FerCanAra/Ce2Lab_ball_and_beam/Ball and Beam/Model 1/images/image 3.jpeg

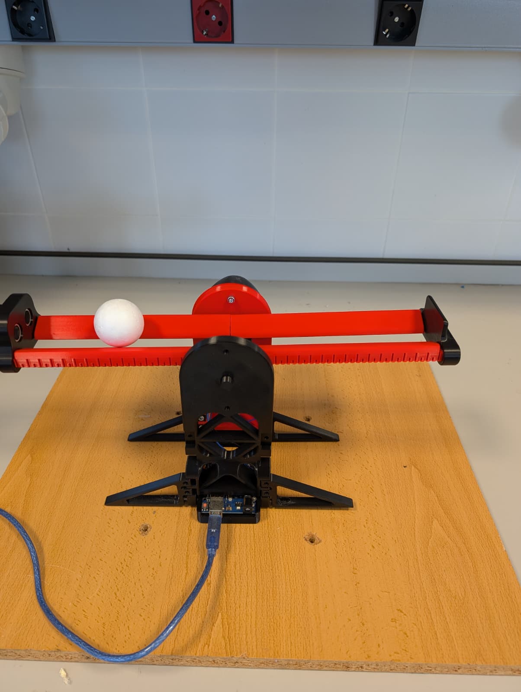
Ball and Beam/Model 1/images/image 3.jpeg
