FerCanAra/Ce2Lab_ball_and_beam/Ball and Beam/Model 1/images/image 7.jpeg

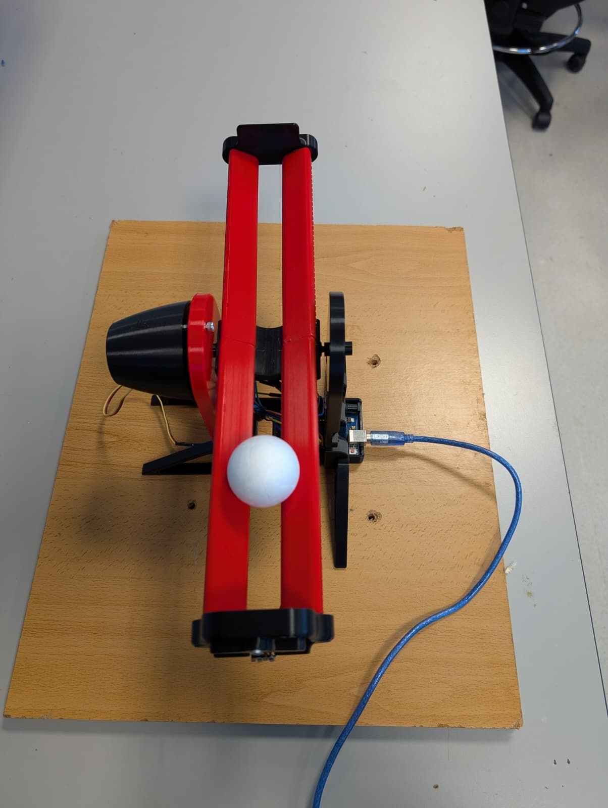
Ball and Beam/Model 1/images/image 7.jpeg
