FerCanAra/Ce2Lab_ball_and_beam/Ball and Beam/Model 1/images/info_3.png

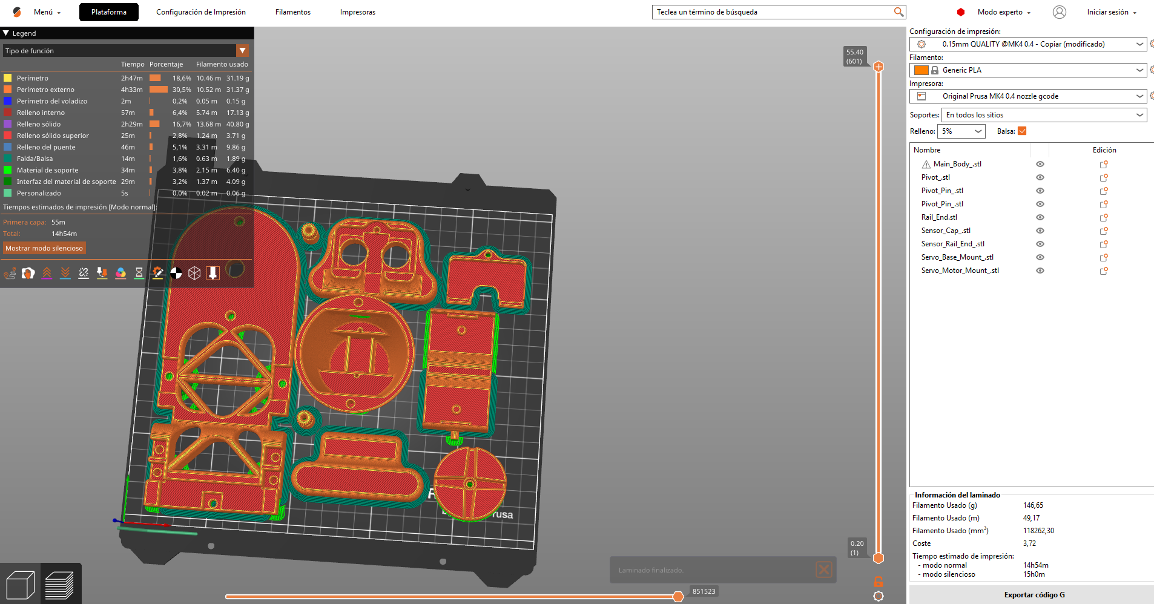
Ball and Beam/Model 1/images/info_3.png
