FerCanAra/Ce2Lab_ball_and_beam/Ball and Beam/Model 2/image/model_2_prusa.png

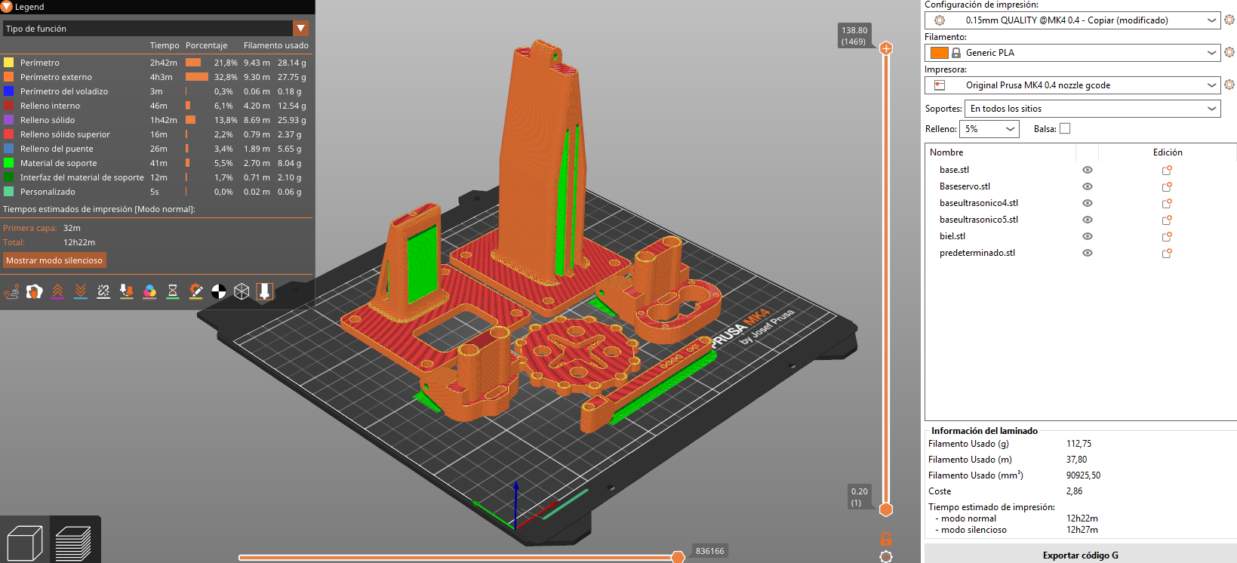
Ball and Beam/Model 2/image/model_2_prusa.png
