FerCanAra/Ce2Lab_ball_and_beam/Watt Governor/stl/Arm_63mm.STL

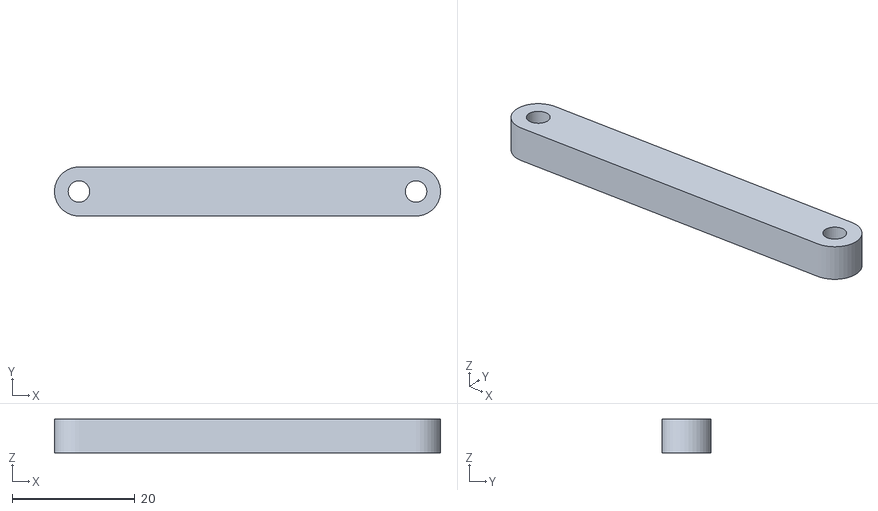
[picture p36: CAD file, 2026-10-01]
Watt Governor/stl/Arm_63mm.STL
63.0 x 8.00 x 5.50
