FerCanAra/Ce2Lab_ball_and_beam/Ball and Beam/Model 2/stl/Servobase.stl

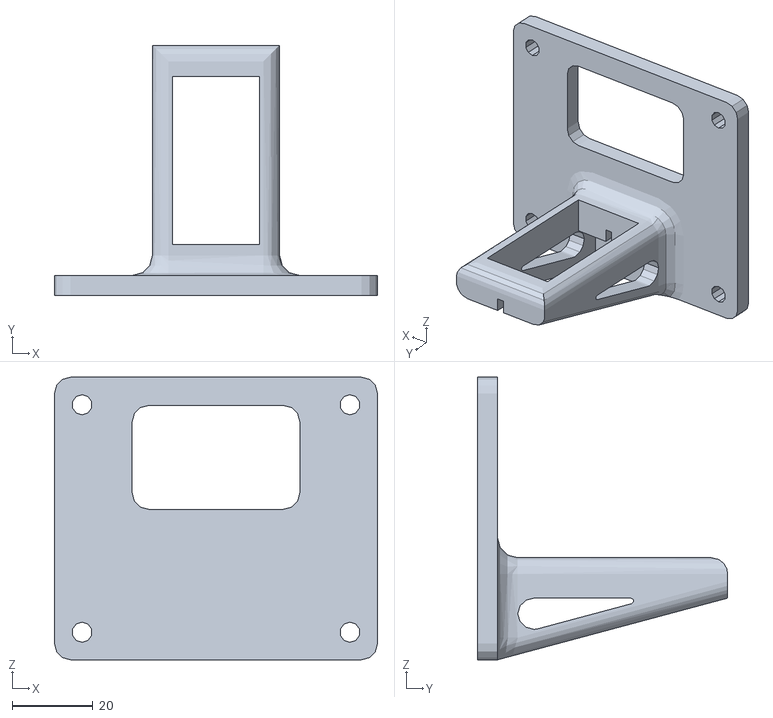
[picture p37: CAD file, 2026-03-30]
Ball and Beam/Model 2/stl/Servobase.stl
80.0 x 62.0 x 70.0
