FerCanAra/Ce2Lab_ball_and_beam/Watt Governor/stl/Base.STL

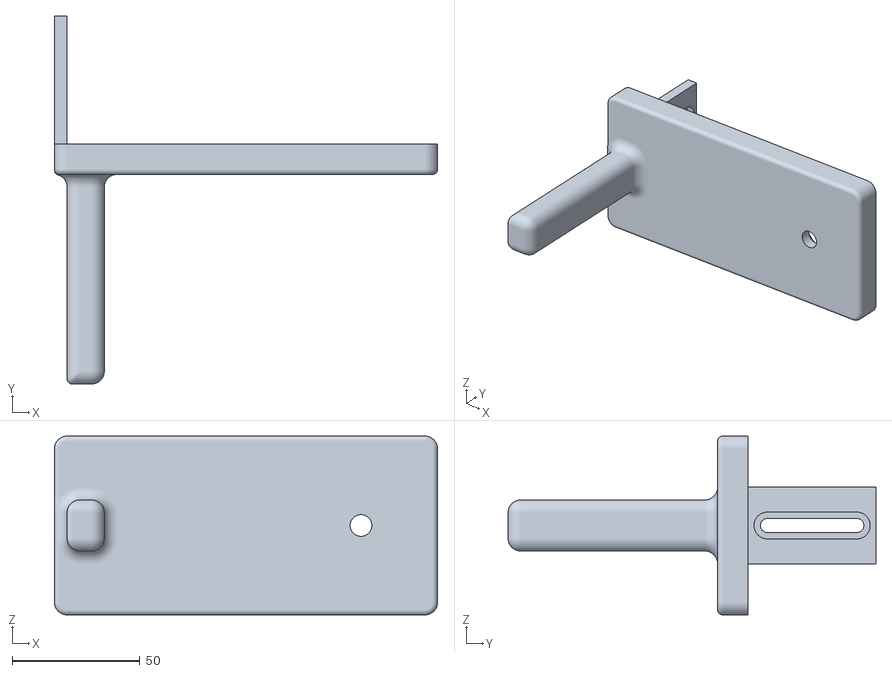
[picture p38: CAD file, 2026-10-01]
Watt Governor/stl/Base.STL
150.0 x 144.0 x 70.0
