FerCanAra/Ce2Lab_ball_and_beam/Ball and Beam/Model 1/stl/Base_Support_Left_.stl

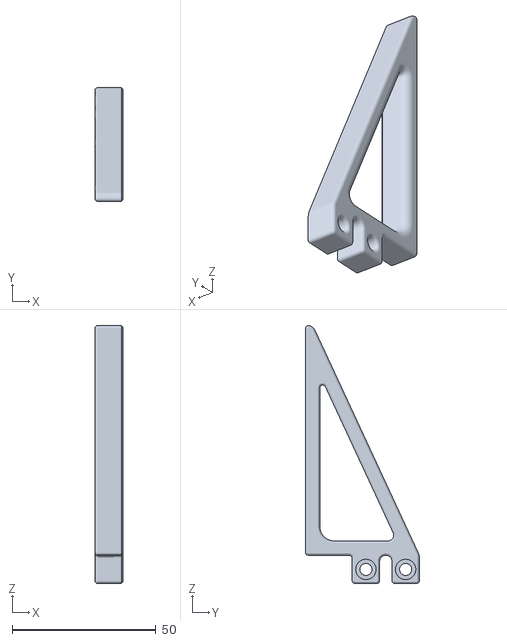
[picture p39: CAD file, 2026-03-13]
Ball and Beam/Model 1/stl/Base_Support_Left_.stl
9.80 x 39.6 x 89.8
