FerCanAra/Ce2Lab_ball_and_beam/Watt Governor/stl/Ball.STL

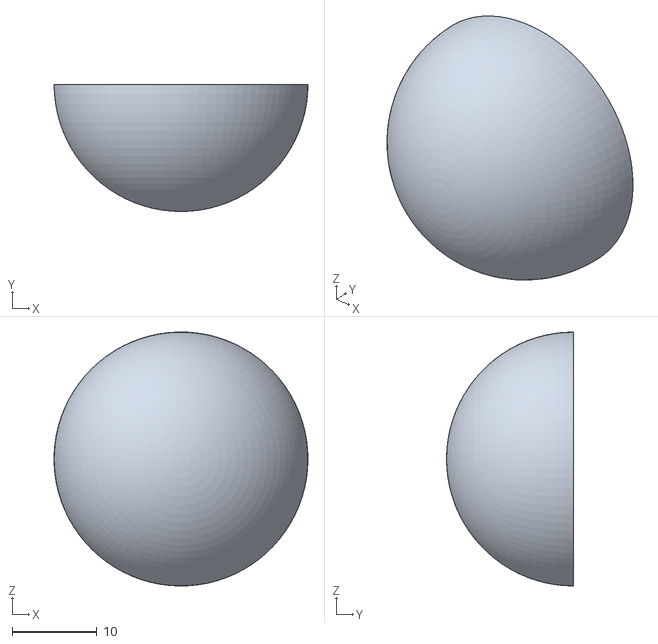
[picture p40: CAD file, 2026-10-01]
Watt Governor/stl/Ball.STL
30.0 x 15.0 x 30.0
