FerCanAra/Ce2Lab_ball_and_beam/Watt Governor/stl/Slider.STL

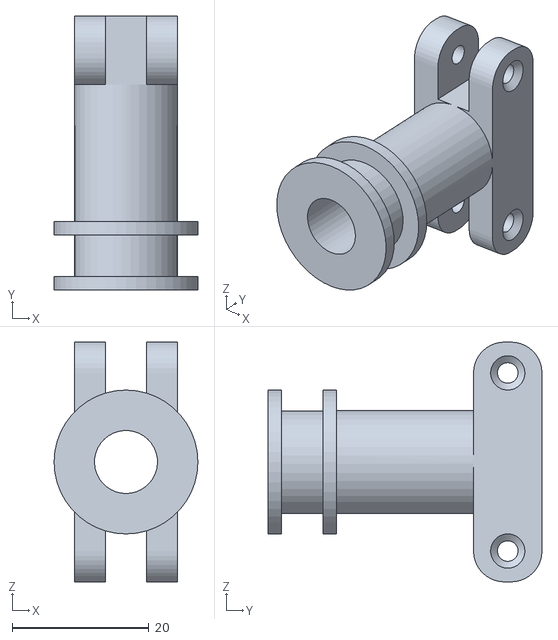
[picture p41: CAD file, 2026-10-01]
Watt Governor/stl/Slider.STL
21.0 x 40.0 x 35.0
