FerCanAra/Ce2Lab_ball_and_beam/Ball and Beam/Model 1/stl/Arduino_Board_Base_.stl

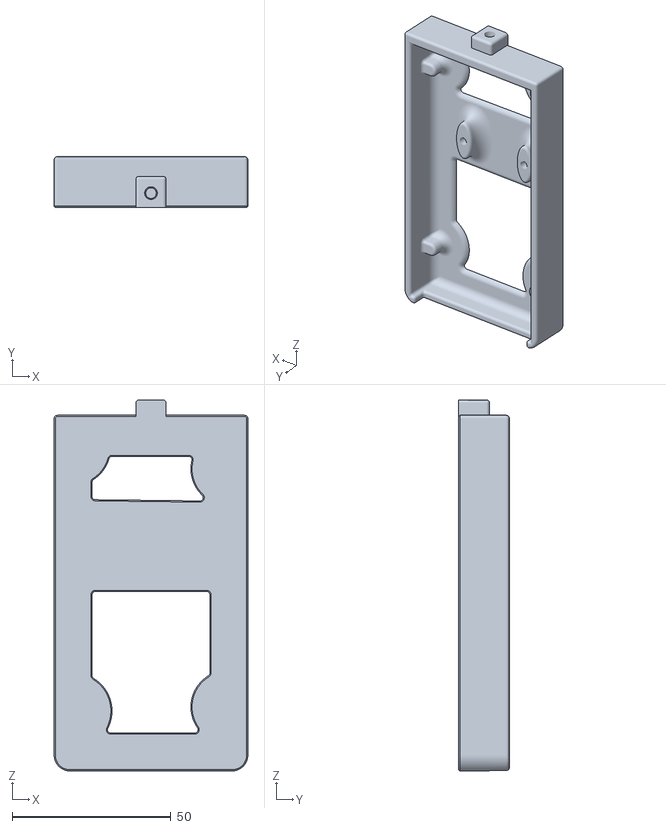
[picture p42: CAD file, 2026-03-13]
Ball and Beam/Model 1/stl/Arduino_Board_Base_.stl
61.0 x 16.0 x 116.8
