FerCanAra/Ce2Lab_ball_and_beam/Watt Governor/stl/Collar.STL

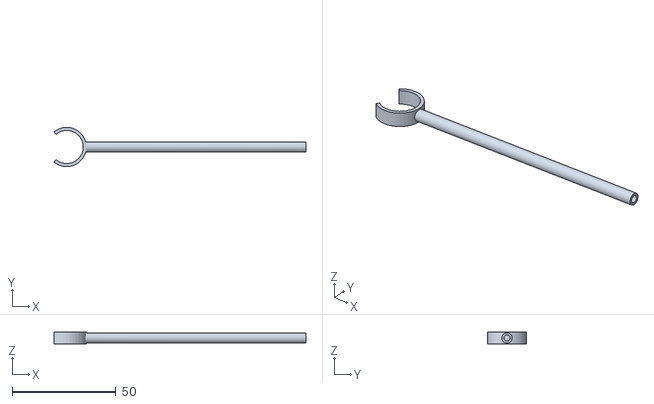
[picture p43: CAD file, 2026-10-01]
Watt Governor/stl/Collar.STL
121.6 x 19.0 x 5.99
