FerCanAra/Ce2Lab_ball_and_beam/Ball and Beam/Model 1/stl/Rail_.step

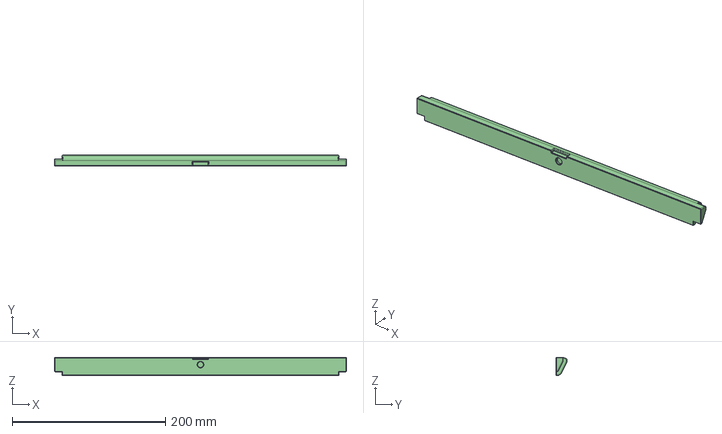
[picture p44: CAD file, 2026-03-13]
Ball and Beam/Model 1/stl/Rail_.step
381.0 x 14.5 x 24.0 mm
