FerCanAra/Ce2Lab_ball_and_beam/Watt Governor/stl/Arm.STL

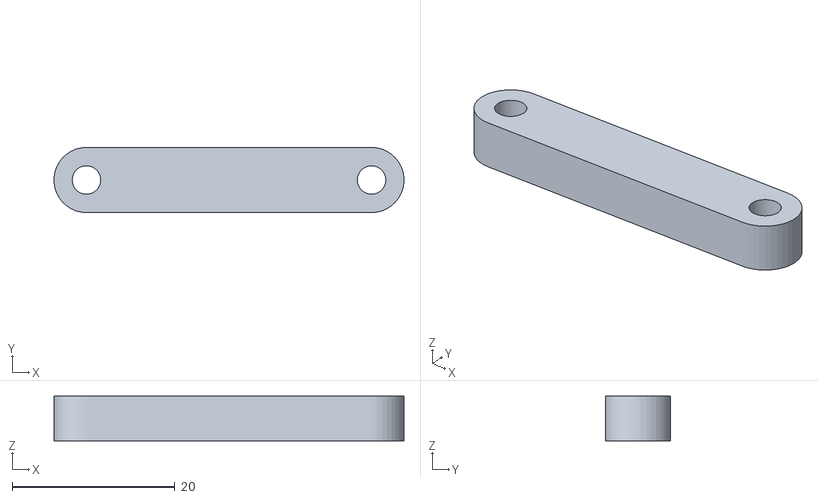
[picture p45: CAD file, 2026-10-01]
Watt Governor/stl/Arm.STL
43.0 x 8.00 x 5.50
