FerCanAra/Ce2Lab_ball_and_beam/Watt Governor/stl/Arm_couple.STL

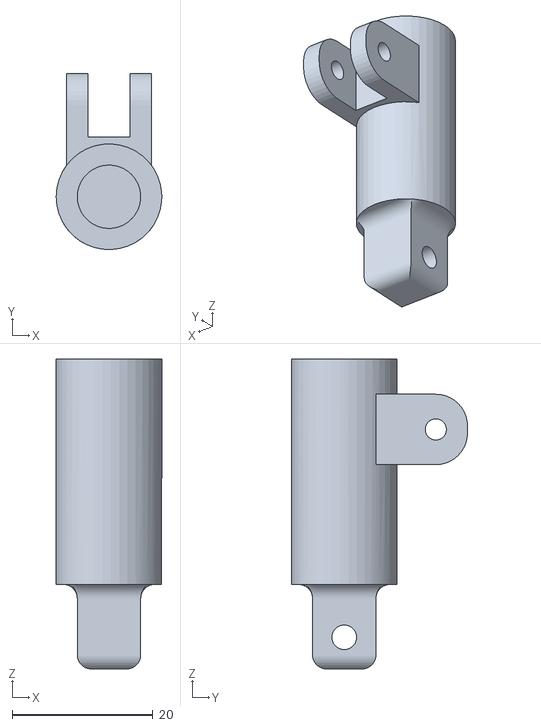
[picture p46: CAD file, 2026-10-01]
Watt Governor/stl/Arm_couple.STL
15.0 x 25.0 x 44.0
