FerCanAra/Ce2Lab_ball_and_beam/Ball and Beam/Model 1/stl/Pivot_Pin_2.STL

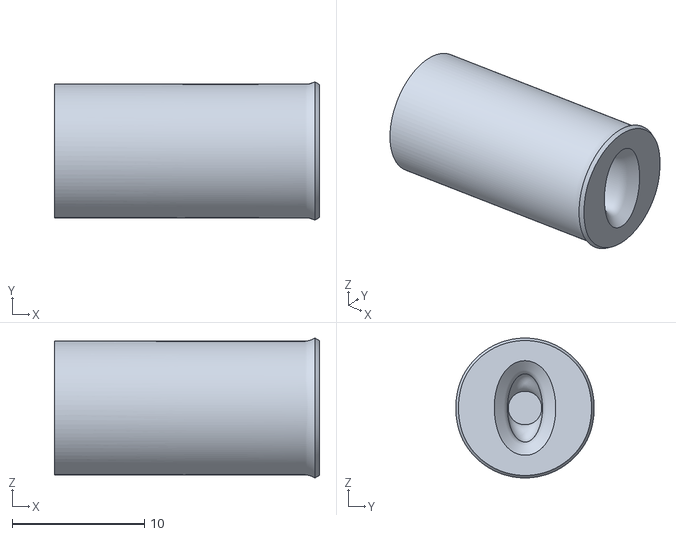
[picture p47: CAD file, 2026-03-13]
Ball and Beam/Model 1/stl/Pivot_Pin_2.STL
20.0 x 10.5 x 10.6
