FerCanAra/Ce2Lab_ball_and_beam/Watt Governor/stl/Dial.STL

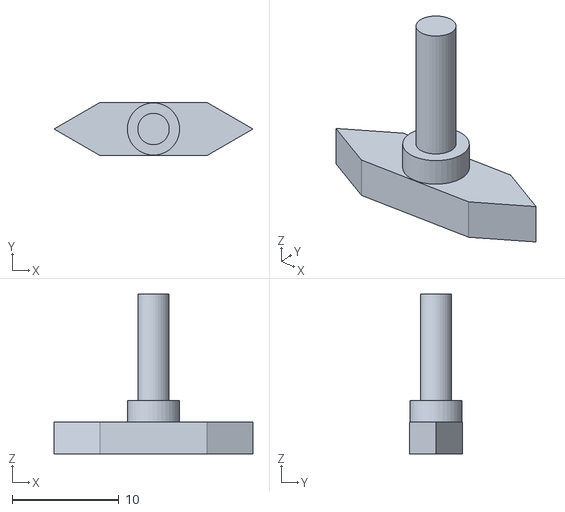
[picture p48: CAD file, 2026-10-01]
Watt Governor/stl/Dial.STL
18.7 x 5.00 x 15.0
