FerCanAra/Ce2Lab_ball_and_beam/Watt Governor/stl/Arm_53mm_.STL

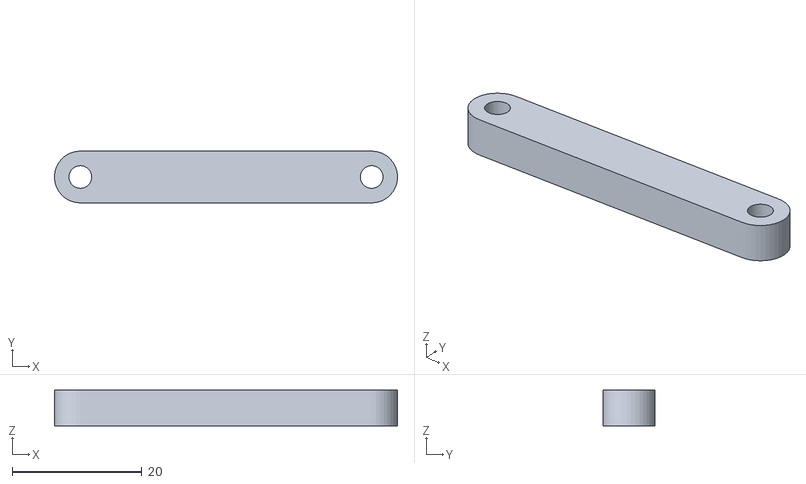
[picture p49: CAD file, 2026-10-01]
Watt Governor/stl/Arm_53mm_.STL
53.0 x 8.00 x 5.50
