FerCanAra/Ce2Lab_ball_and_beam/Ball and Beam/Model 1/stl/Breadboard_Bracket_Print_x2.stl

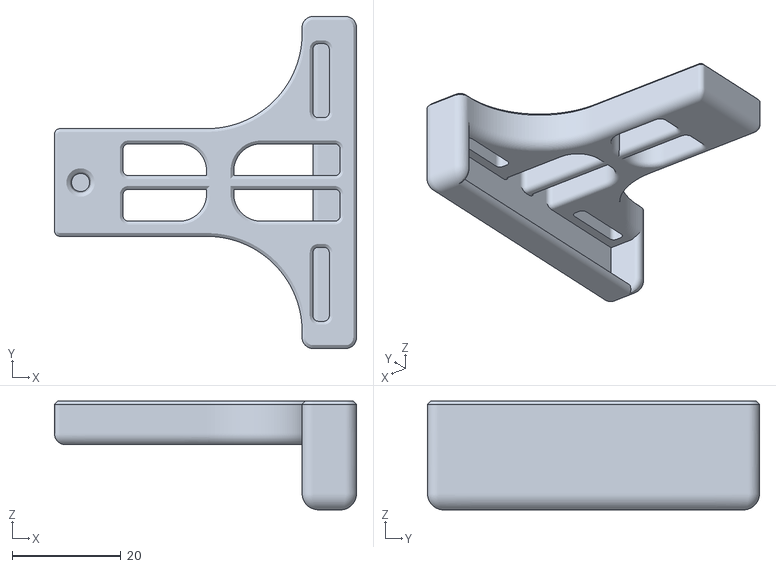
[picture p50: CAD file, 2026-03-13]
Ball and Beam/Model 1/stl/Breadboard_Bracket_Print_x2.stl
55.5 x 61.0 x 20.0
