FerCanAra/Ce2Lab_ball_and_beam/Ball and Beam/Model 1/stl/Servo_Base_Mount_.STL

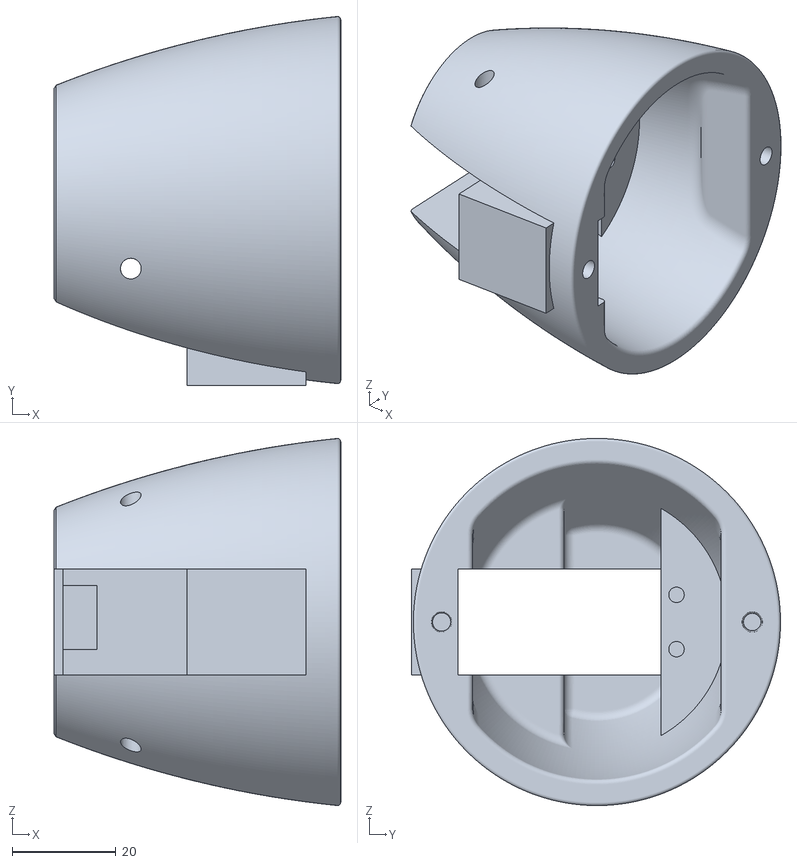
[picture p51: CAD file, 2026-03-13]
Ball and Beam/Model 1/stl/Servo_Base_Mount_.STL
55.3 x 71.3 x 70.9
