FerCanAra/Ce2Lab_ball_and_beam/Ball and Beam/Model 1/stl/Pivot.STL

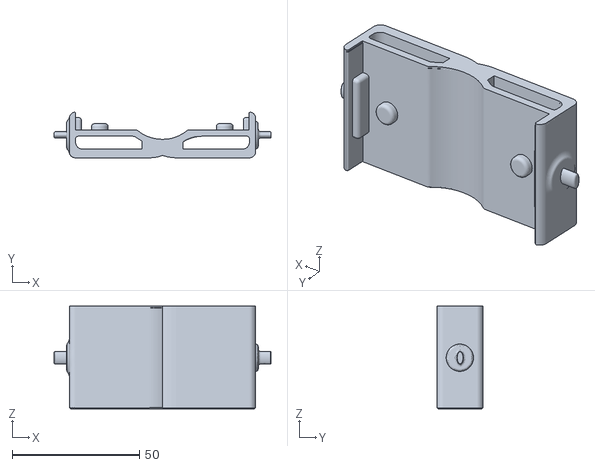
[picture p52: CAD file, 2026-03-13]
Ball and Beam/Model 1/stl/Pivot.STL
85.1 x 17.9 x 40.2
