FerCanAra/Ce2Lab_ball_and_beam/Ball and Beam/Model 1/stl/Servo_Motor_Mount_.stl

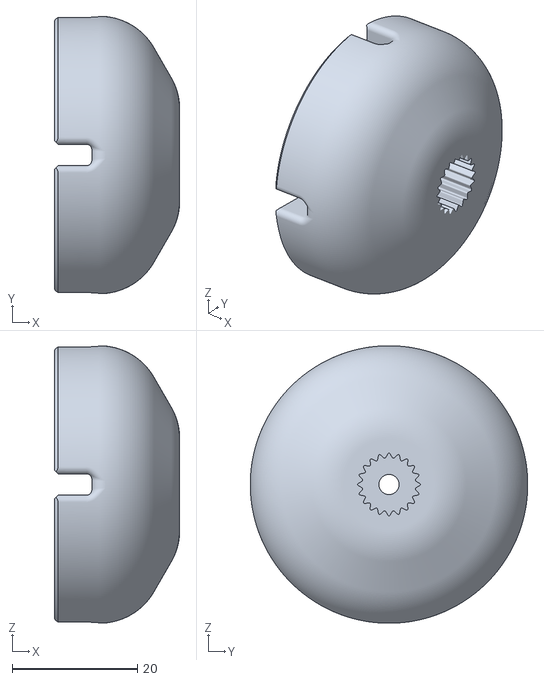
[picture p53: CAD file, 2026-03-13]
Ball and Beam/Model 1/stl/Servo_Motor_Mount_.stl
20.0 x 44.2 x 44.2
