FerCanAra/Ce2Lab_ball_and_beam/Ball and Beam/Model 1/stl/Rail_End.stl

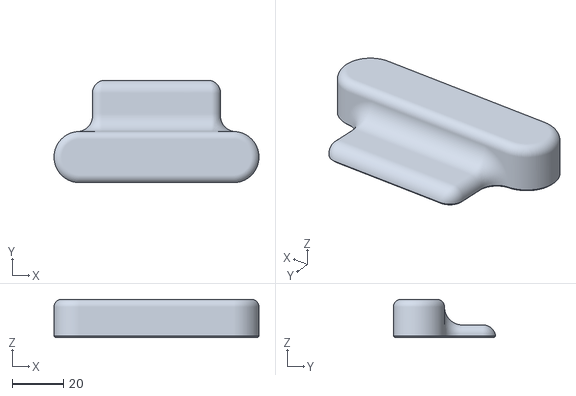
[picture p54: CAD file, 2026-03-13]
Ball and Beam/Model 1/stl/Rail_End.stl
80.0 x 40.0 x 15.0
